seler1500/SeLNA-v2/sweeps/selna-L-NF-Gain___FSV3000_ScreenShot_2026-06-27_10-09-03.PNG

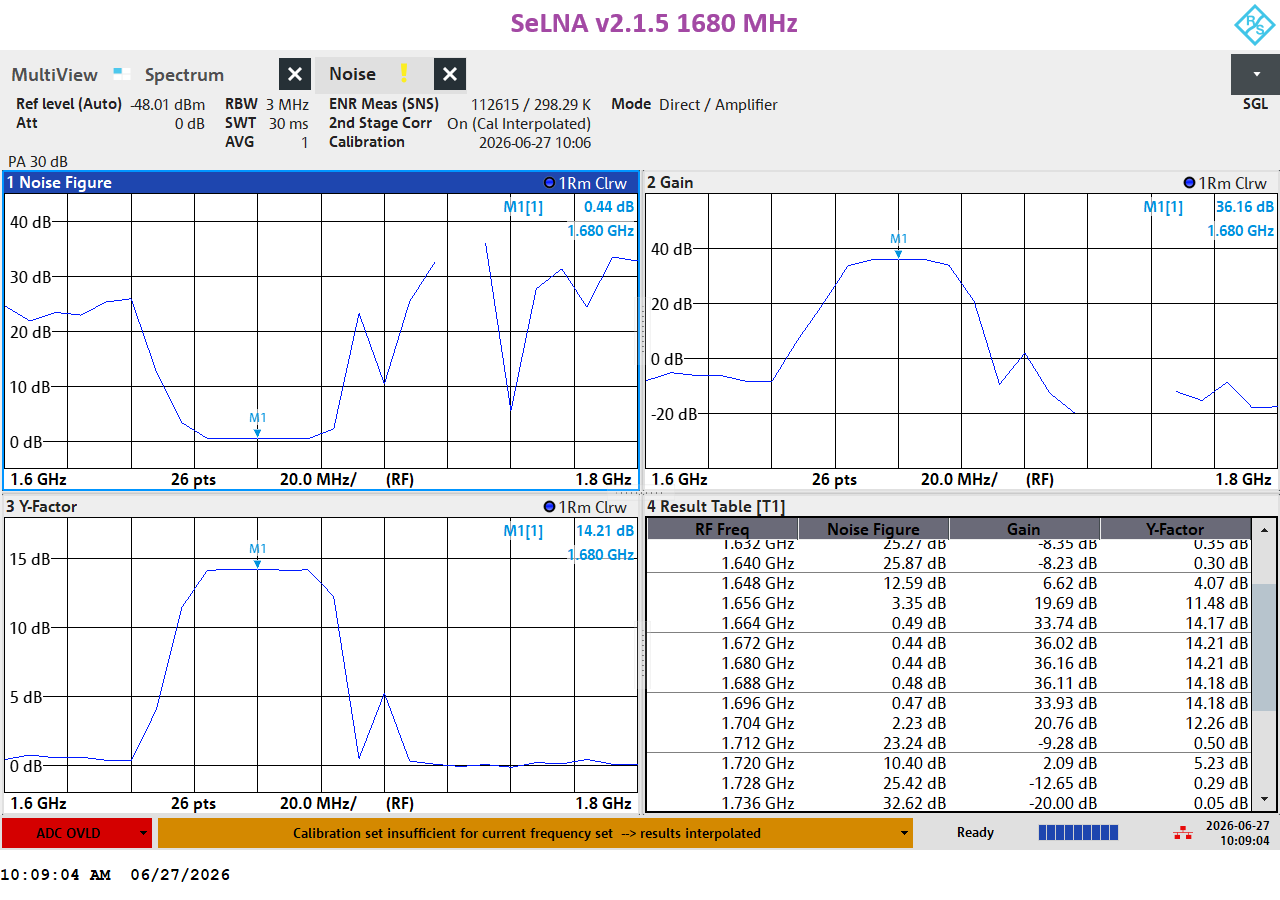
sweeps/selna-L-NF-Gain___FSV3000_ScreenShot_2026-06-27_10-09-03.PNG
