seler1500/SeLNA-v2/sweeps/selna-L-p1db___ZNL_ScreenShot_2026-06-27_10-24-55.PNG

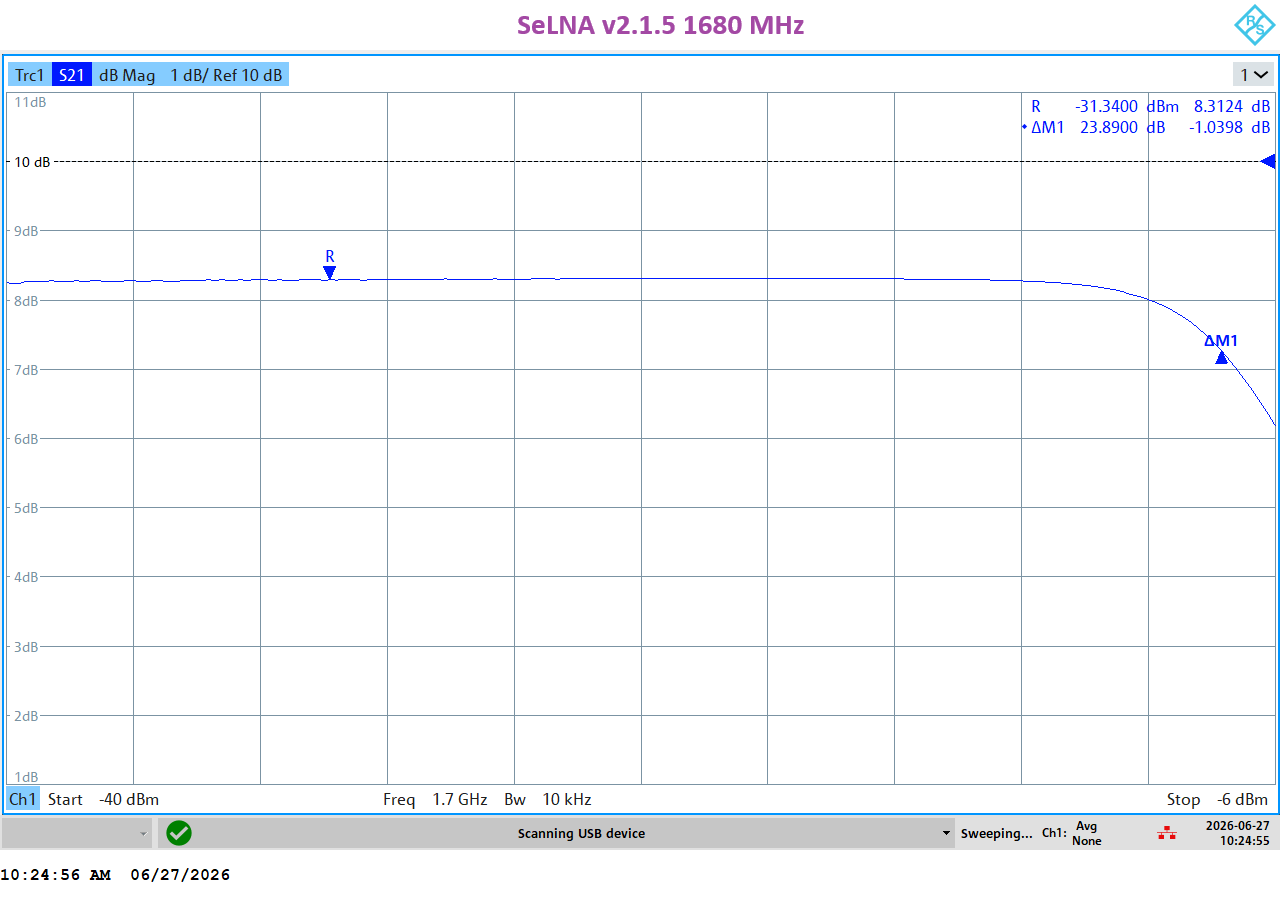
sweeps/selna-L-p1db___ZNL_ScreenShot_2026-06-27_10-24-55.PNG
