seler1500/SeLNA-v2/sweeps/selna-S-NF-Gain___FSV3000_ScreenShot_2026-06-27_10-17-11.PNG

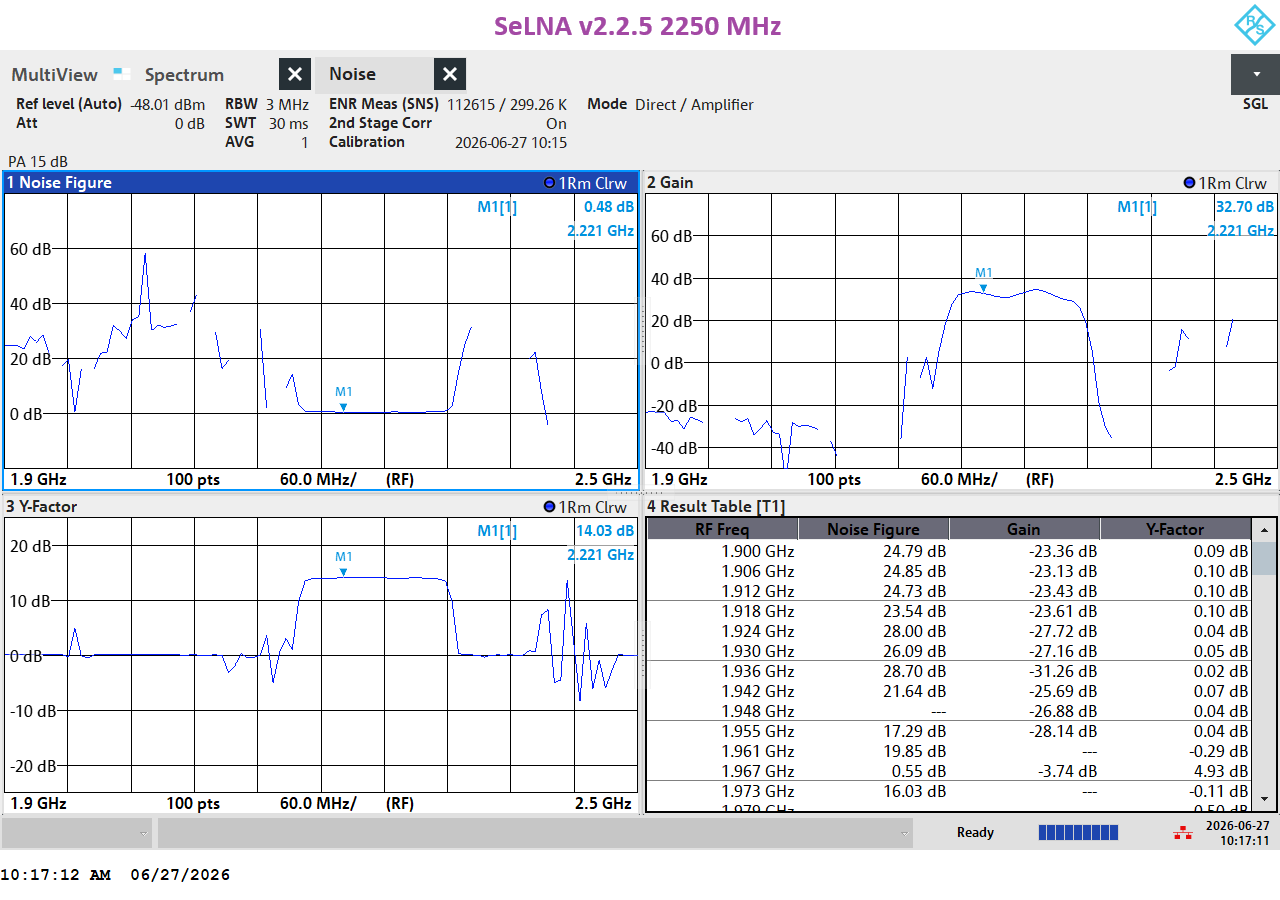
sweeps/selna-S-NF-Gain___FSV3000_ScreenShot_2026-06-27_10-17-11.PNG
