seler1500/SeLNA-v2/sweeps/SF33M6-1700.000-F30IL03AL.png

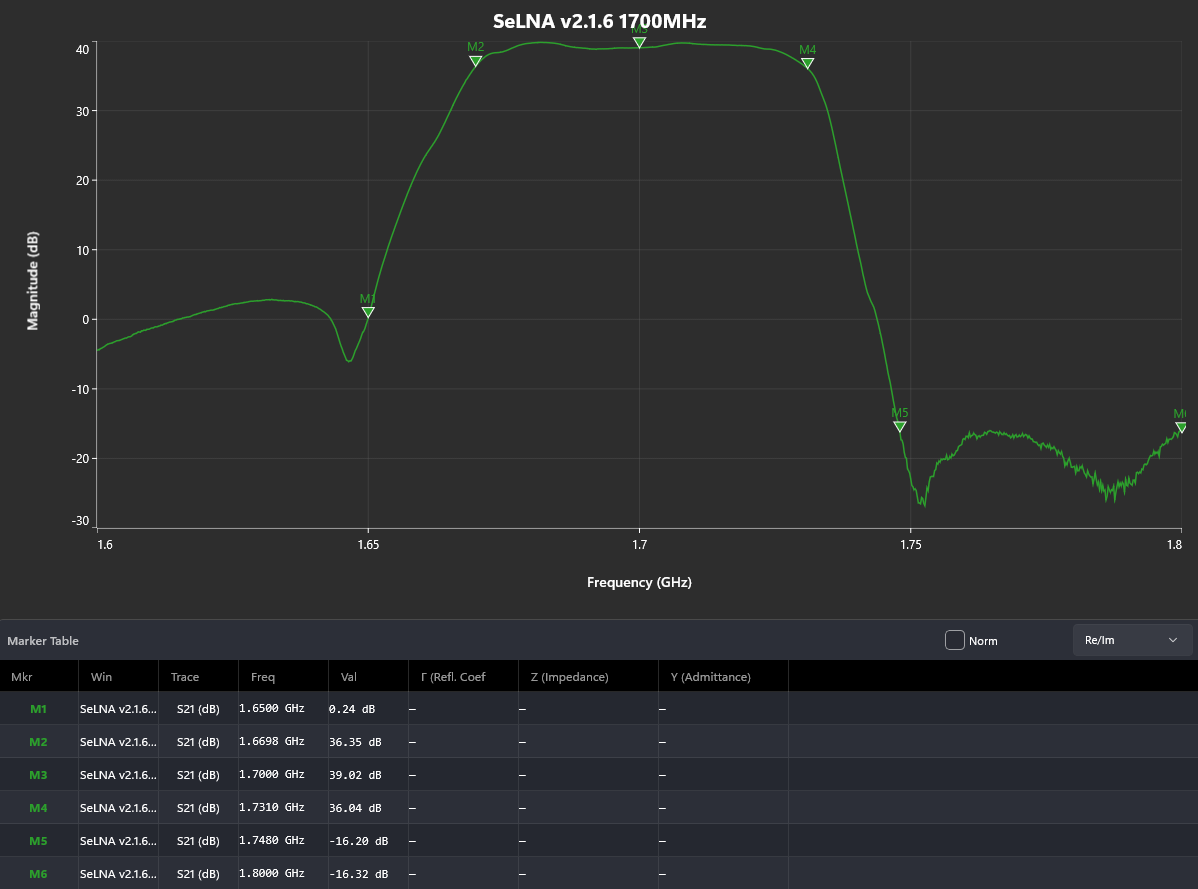
sweeps/SF33M6-1700.000-F30IL03AL.png
