seler1500/SeLNA-v2/sweeps/TA0515A.png

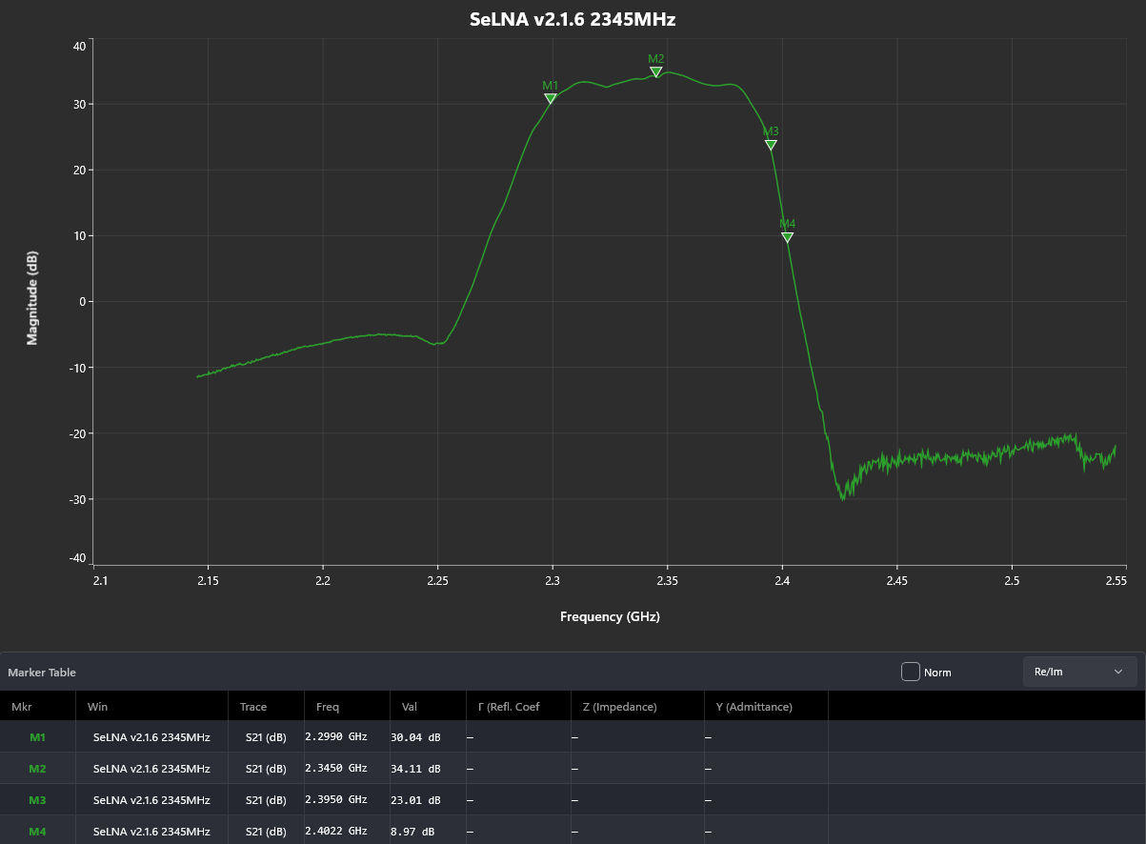
sweeps/TA0515A.png
