seler1500/SeLNA-v2/sweeps/TA0700A.png

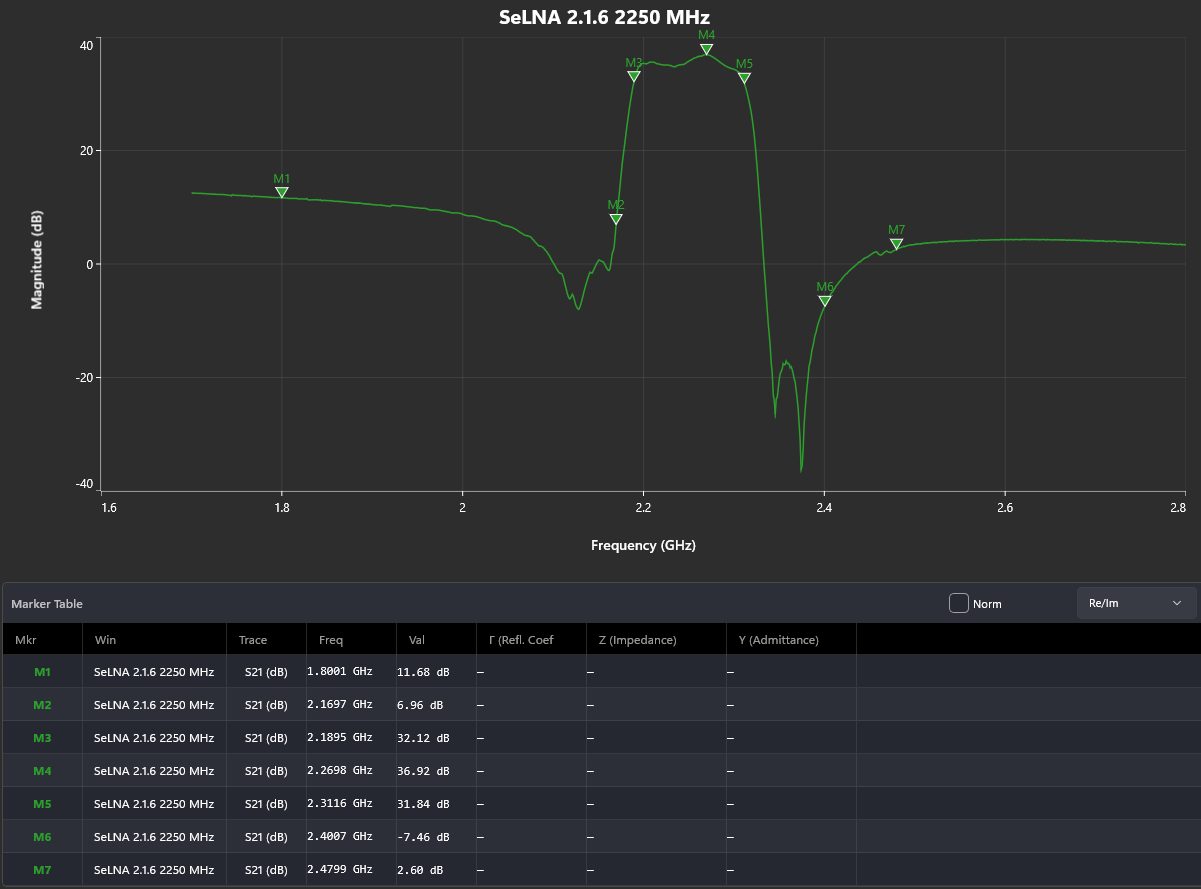
sweeps/TA0700A.png
