seler1500/SeLNA-v2/sweeps/TA1583A-elektro.png

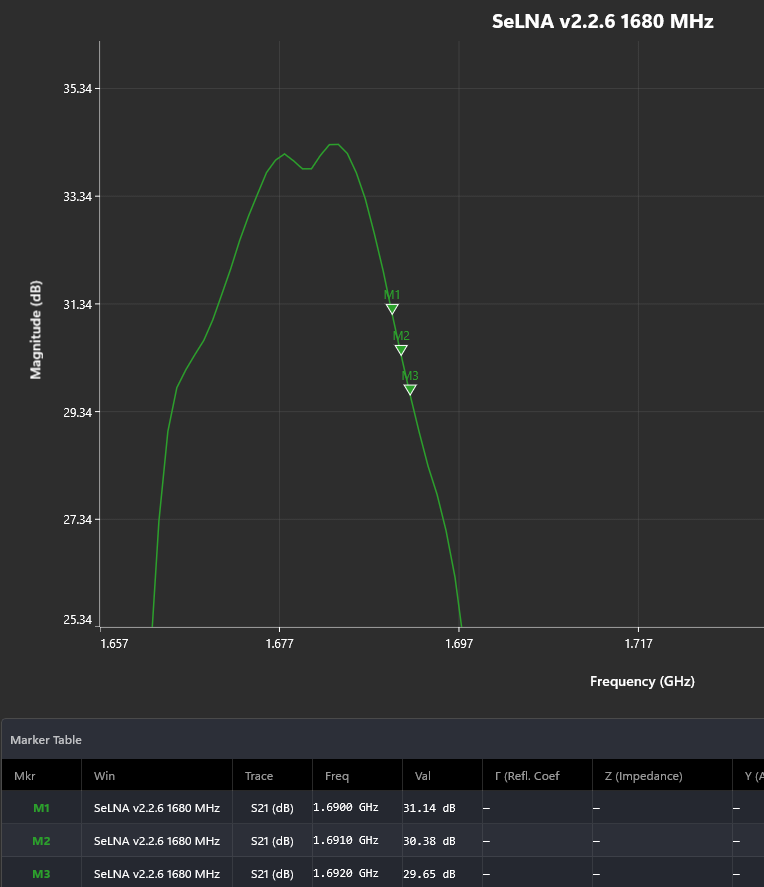
sweeps/TA1583A-elektro.png
