seler1500/SeLNA-v2/sweeps/TA2019A.png

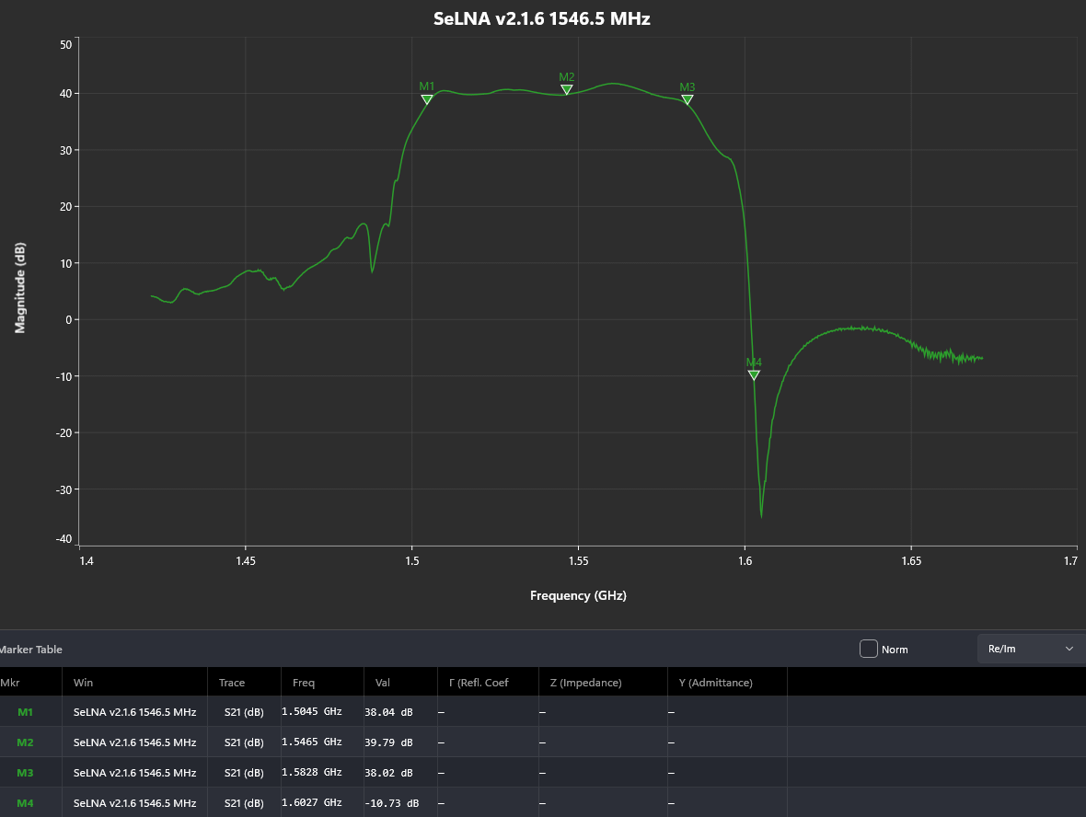
sweeps/TA2019A.png
