seler1500/SeLNA-v2/sweeps/TA2544A.png

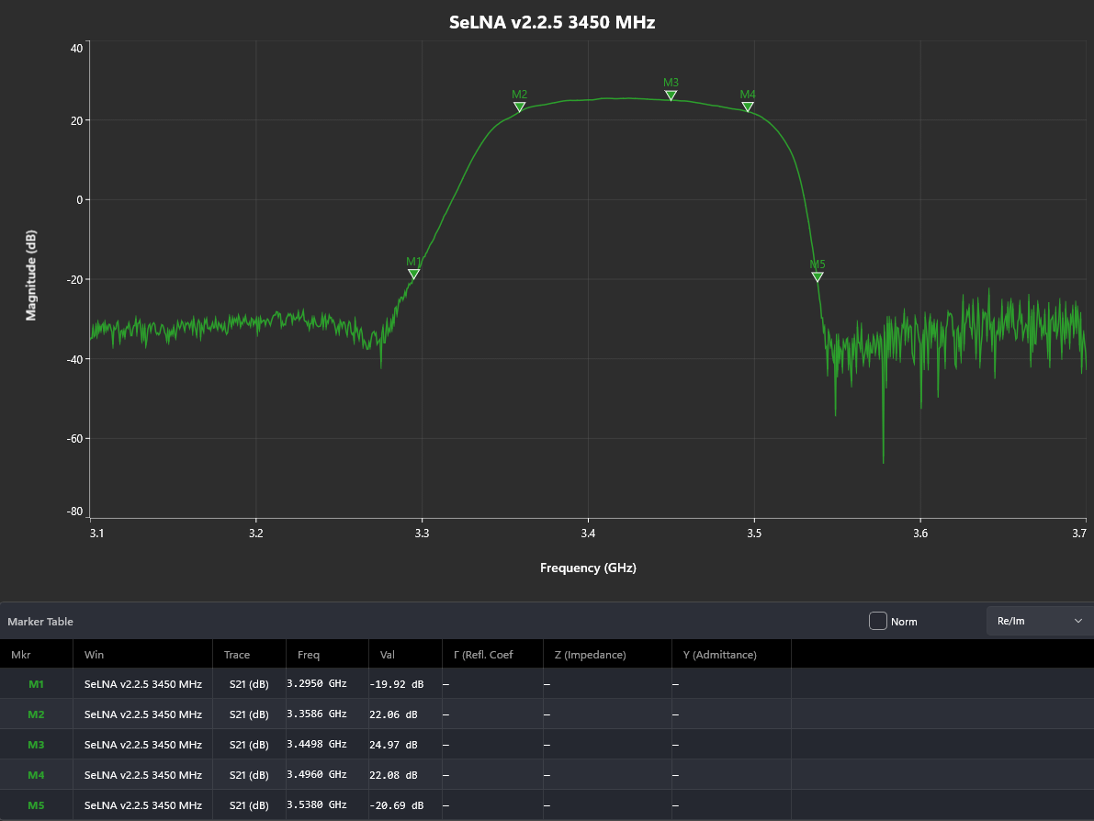
sweeps/TA2544A.png
