seler1500/SeLNA-v2/sweeps/TA2727AA3112.png

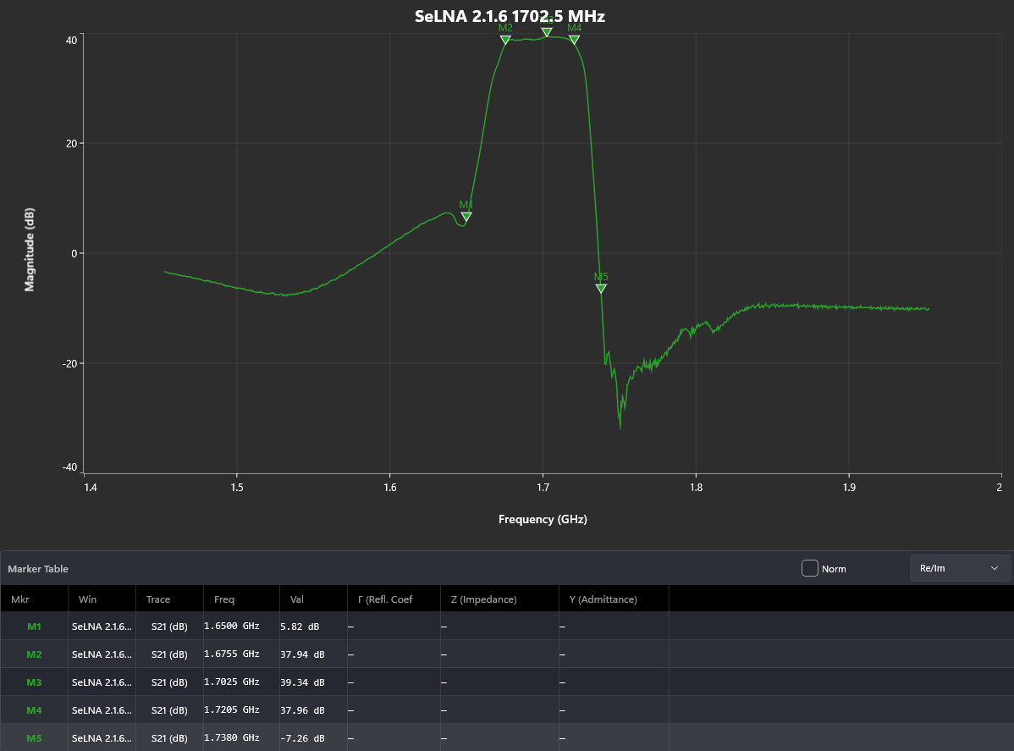
sweeps/TA2727AA3112.png
